naitikshukla/drone/frames/camera-plate-down-1.stl

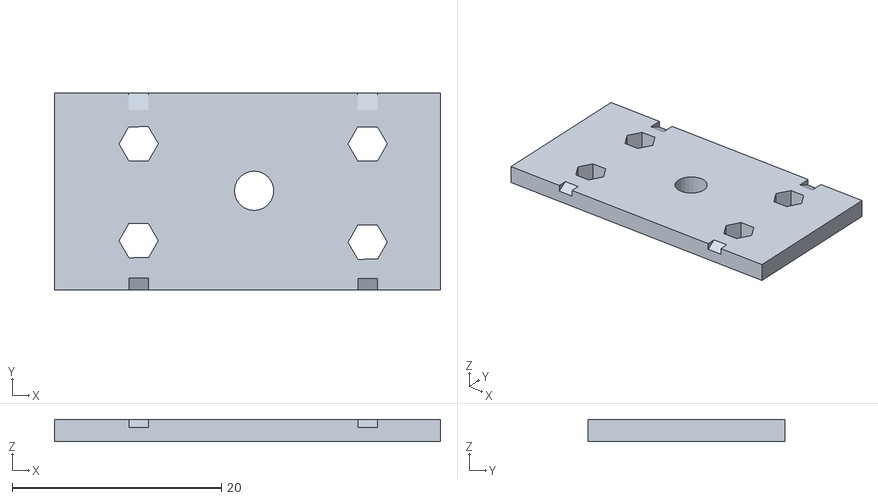
[picture p43: CAD file, 2017-04-28]
frames/camera-plate-down-1.stl
36.9 x 18.8 x 2.13
