naitikshukla/drone/frames/camera-plate-down-2.stl

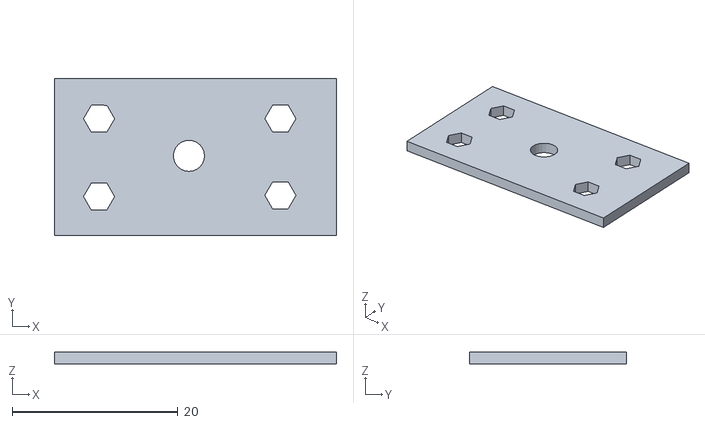
[picture p44: CAD file, 2017-04-28]
frames/camera-plate-down-2.stl
34.0 x 19.0 x 1.49
