naitikshukla/drone/frames/camera-plate-down-clips.stl

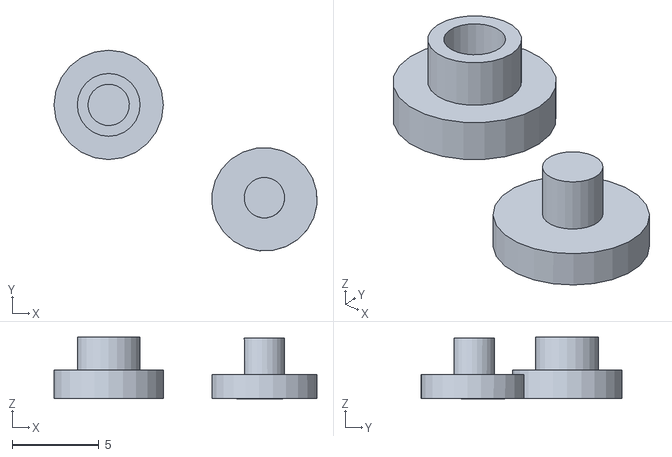
[picture p45: CAD file, 2017-04-28]
frames/camera-plate-down-clips.stl
15.2 x 11.6 x 3.56
