naitikshukla/drone/frames/pi-cover.stl

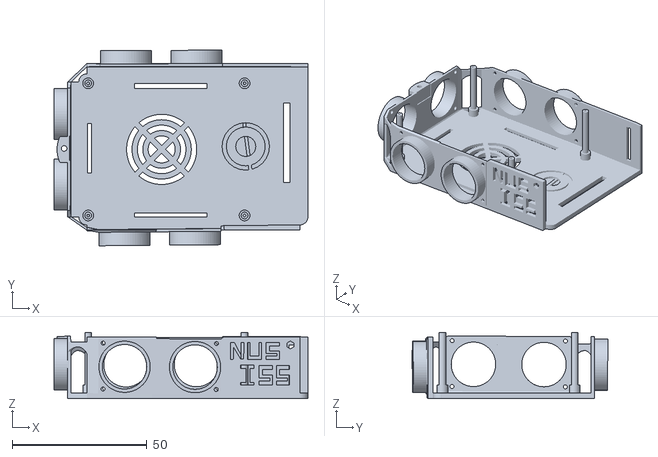
[picture p46: CAD file, 2017-04-22]
frames/pi-cover.stl
94.2 x 72.5 x 24.5
