naitikshukla/drone/frames/nus-iss.stl

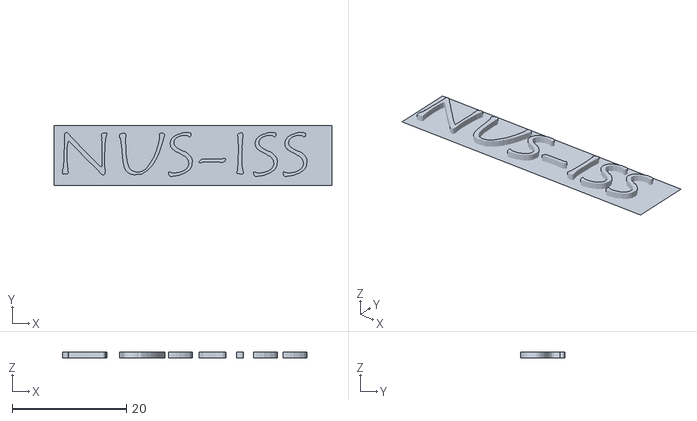
[picture p47: CAD file, 2017-04-08]
frames/nus-iss.stl
48.6 x 10.6 x 1
