naitikshukla/drone/frames/side-plate-non-hole.stl

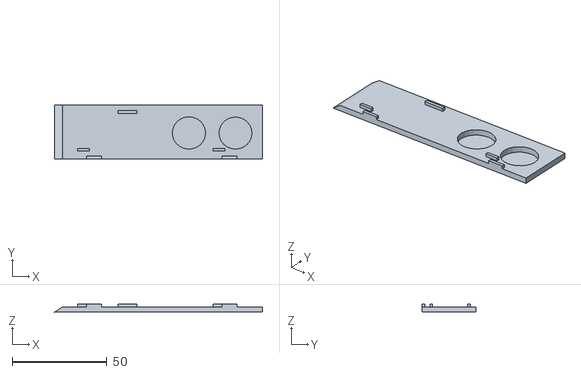
[picture p48: CAD file, 2017-04-08]
frames/side-plate-non-hole.stl
109.6 x 28.3 x 4.30
