naitikshukla/drone/frames/side-plate-cover.stl

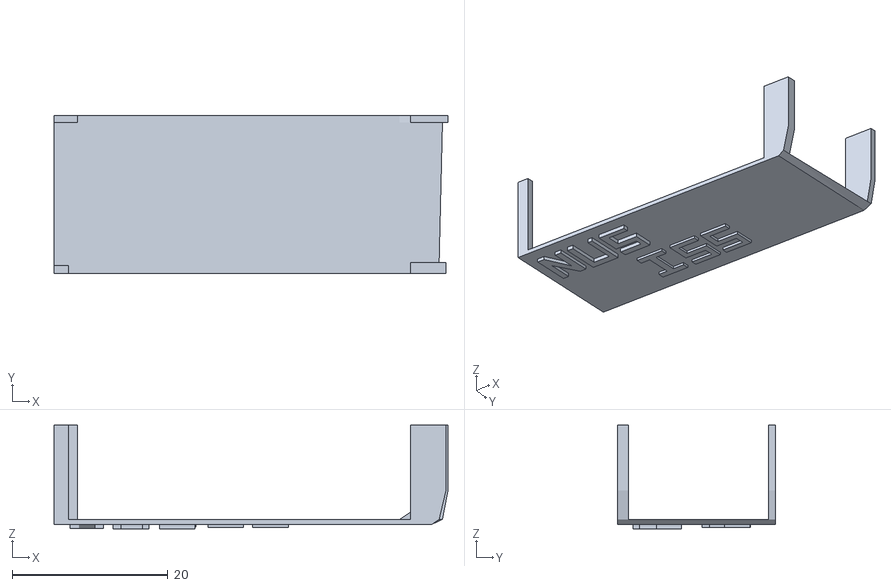
[picture p49: CAD file, 2017-04-08]
frames/side-plate-cover.stl
50.6 x 20.4 x 13.3
