naitikshukla/drone/frames/side-plate-with-hole.stl

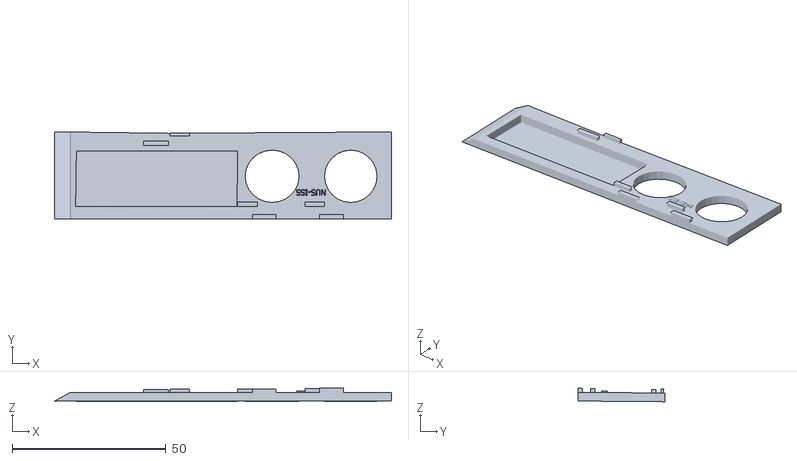
[picture p50: CAD file, 2017-04-08]
frames/side-plate-with-hole.stl
109.6 x 28.4 x 4.41
