naitikshukla/drone/frames/side-plate-front-hole.stl

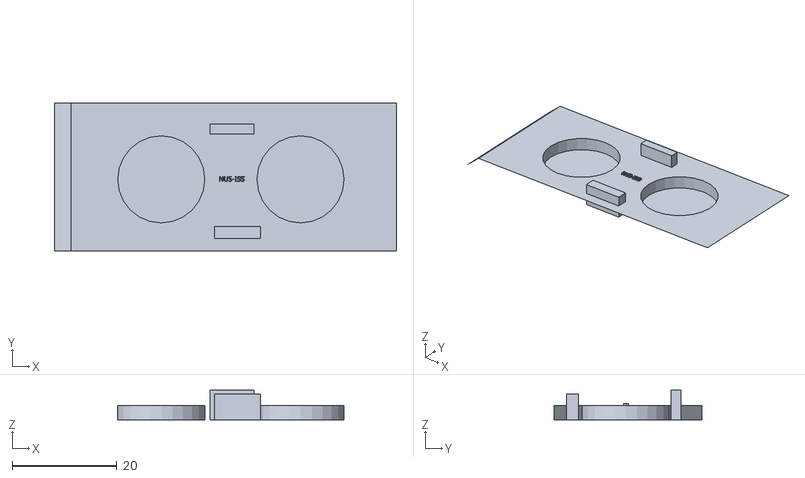
[picture p51: CAD file, 2017-04-08]
frames/side-plate-front-hole.stl
65.3 x 28.3 x 5.64
