naitikshukla/drone/frames/custwing1.stl

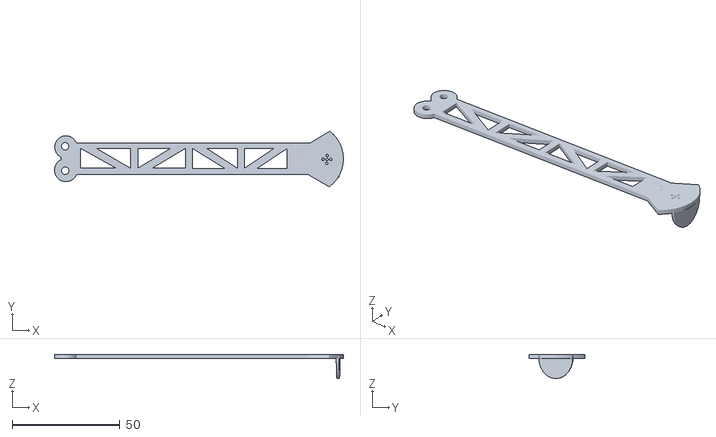
[picture p52: CAD file, 2017-04-02]
frames/custwing1.stl
134.1 x 25.8 x 11.3
