naitikshukla/drone/frames/plate3.stl

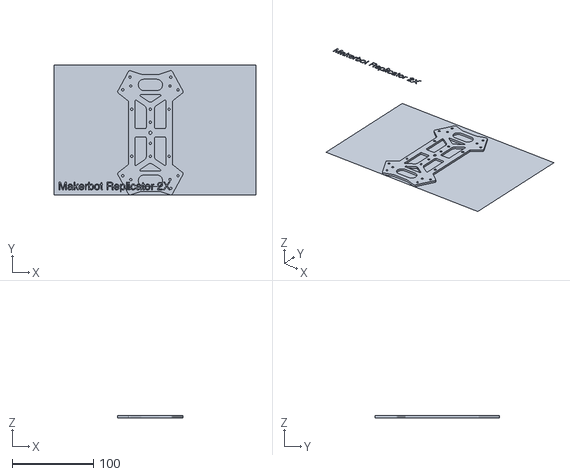
[picture p53: CAD file, 2017-04-02]
frames/plate3.stl
248.9 x 160.0 x 149.9
