naitikshukla/drone/frames/plate1.stl

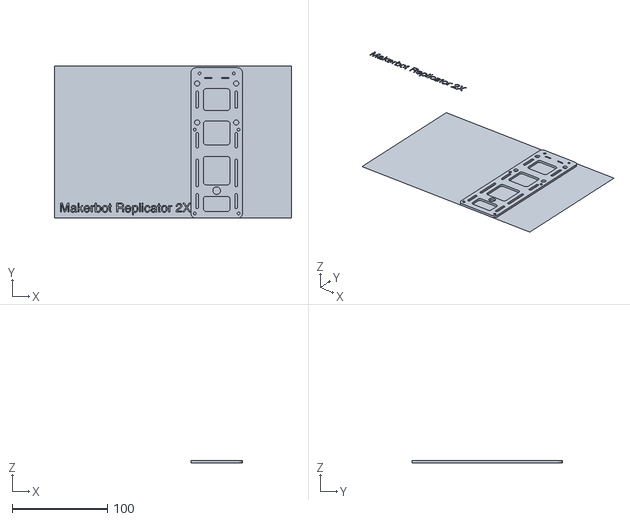
[picture p54: CAD file, 2017-04-02]
frames/plate1.stl
248.9 x 160.0 x 149.9
