naitikshukla/drone/frames/clips.stl

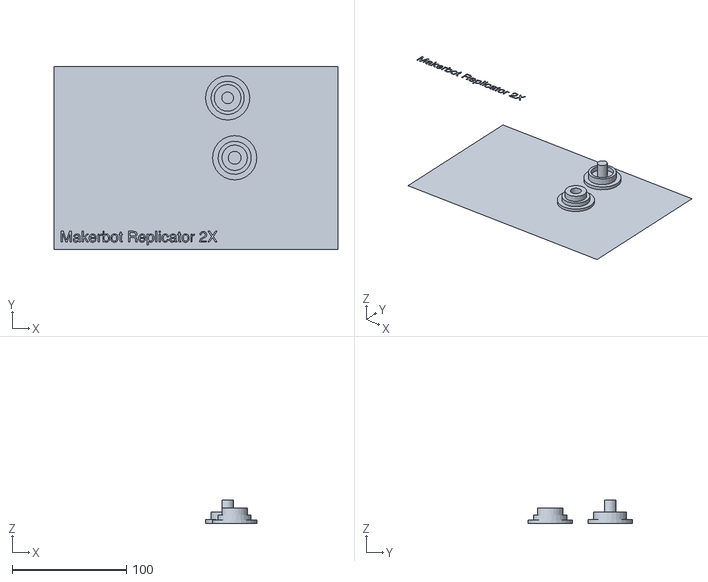
[picture p55: CAD file, 2017-04-02]
frames/clips.stl
248.9 x 160.0 x 149.9
