naitikshukla/drone/frames/plate2.stl

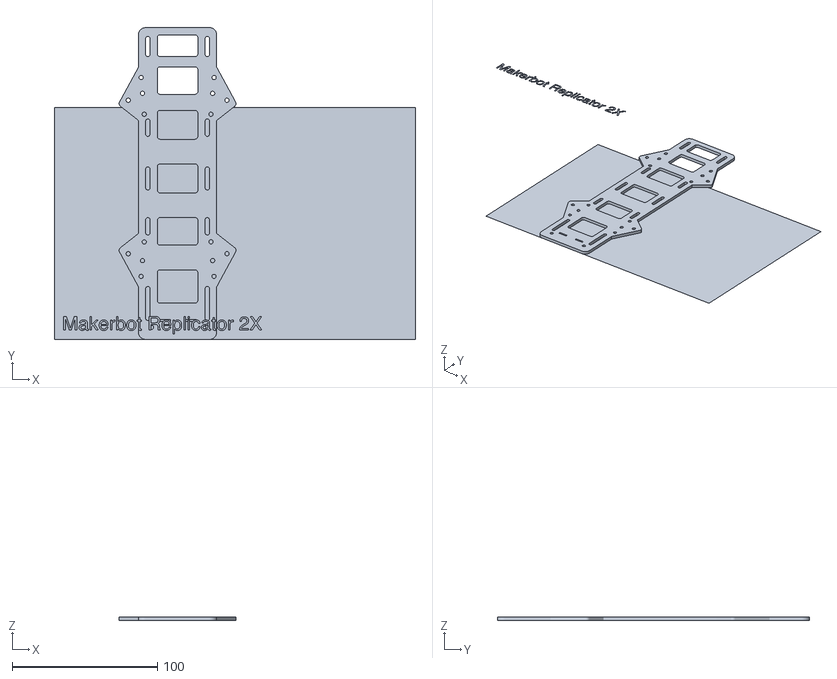
[picture p56: CAD file, 2017-04-02]
frames/plate2.stl
248.9 x 215.0 x 149.9
