naitikshukla/drone/frames/pillar.stl

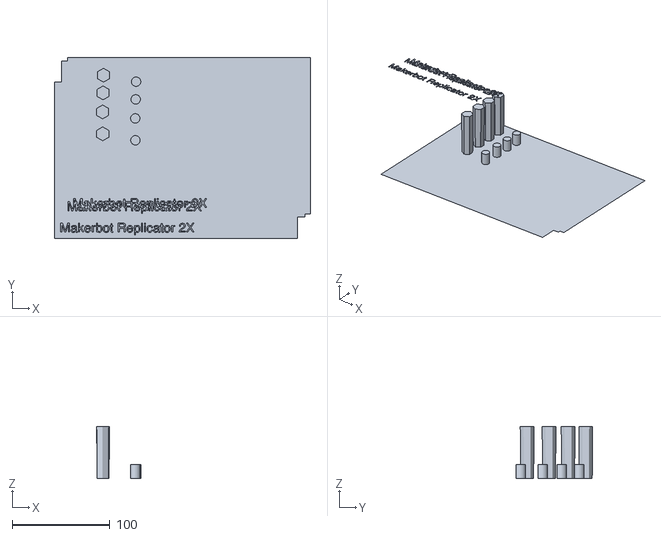
[picture p57: CAD file, 2017-04-02]
frames/pillar.stl
262.0 x 185.1 x 149.9
